dohn-joh/liaison/ergogen/output/outlines/pcb_left.dxf

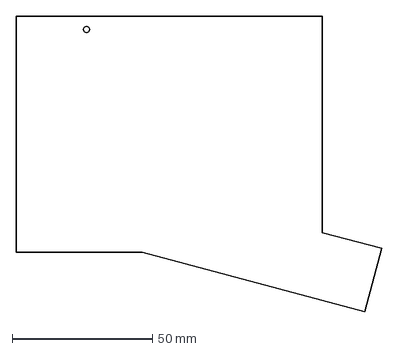
[picture p17: CAD file, 2024-09-29]
ergogen/output/outlines/pcb_left.dxf
130.3 x 105.3 mm
