dohn-joh/liaison/ergogen/output/outlines/screws.dxf

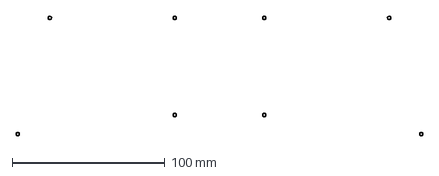
[picture p18: CAD file, 2024-09-29]
ergogen/output/outlines/screws.dxf
266.2 x 78.2 mm
